itoroc/DetectorRadiacionRemoto/Diagramas_Electrónicos/ConsolaDeControl.kicad_sch

## KiCad design Diagramas_Electrónicos/ConsolaDeControl.kicad_sch (2025-11-12)

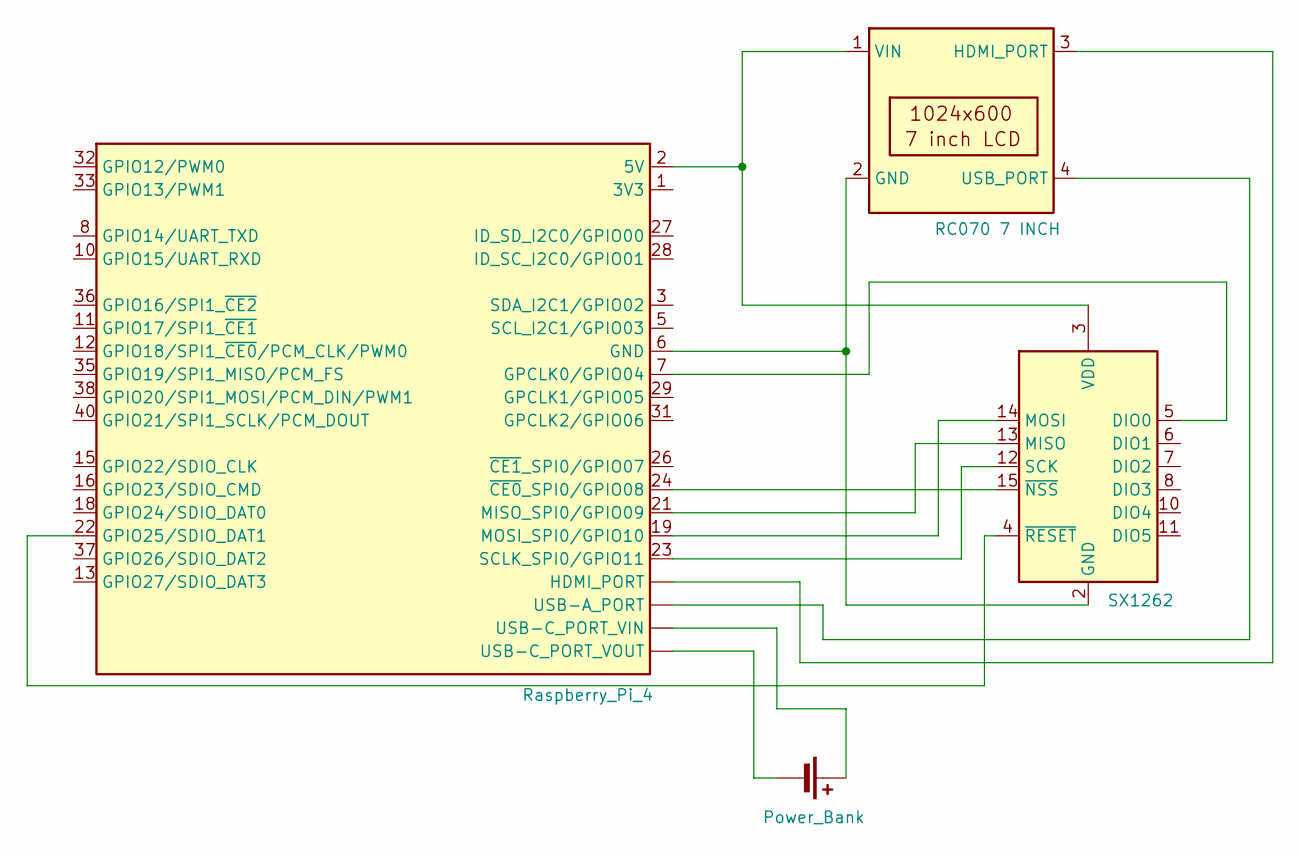
[picture p7: schematic ConsolaDeControl.kicad_sch]

Parts:
BT1: Power_Bank
J1: Raspberry_Pi_4
U1: RC070 7 INCH
U2: SX1262; Ai-Thinker-Ra-01-LoRa

Connections:
unnamed: BT1.1 (+), J1. (HDMI_PORT)
unnamed: BT1.2 (-), J1. (HDMI_PORT)
unnamed: J1.1 (3V3), J1.17 (3V3)
unnamed: J1.2 (5V), J1.4 (5V), U1.1 (VIN), U2.3 (VDD)
unnamed: J1.6 (GND), U1.2 (GND), U2.1 (GND), U2.2 (GND), U2.9 (GND), U2.16 (GND)
unnamed: J1.7 (GPCLK0/GPIO04), U2.5 (DIO0)
unnamed: J1.9 (GND), J1.14 (GND), J1.20 (GND), J1.25 (GND), J1.30 (GND), J1.34 (GND), J1.39 (GND)
unnamed: J1.19 (MOSI_SPI0/GPIO10), U2.14 (MOSI)
unnamed: J1.21 (MISO_SPI0/GPIO09), U2.13 (MISO)
unnamed: J1.22 (GPIO25/SDIO_DAT1), U2.4 (~RESET)
unnamed: J1.23 (SCLK_SPI0/GPIO11), U2.12 (SCK)
unnamed: J1.24 (~CE0_SPI0/GPIO08), U2.15 (~NSS)
unnamed: J1. (HDMI_PORT), U1.3 (HDMI_PORT), U1.4 (USB_PORT)
