itoroc/DetectorRadiacionRemoto/Diagramas_Electrónicos/DetectorRemoto.kicad_sch

## KiCad design Diagramas_Electrónicos/DetectorRemoto.kicad_sch (2025-11-12)

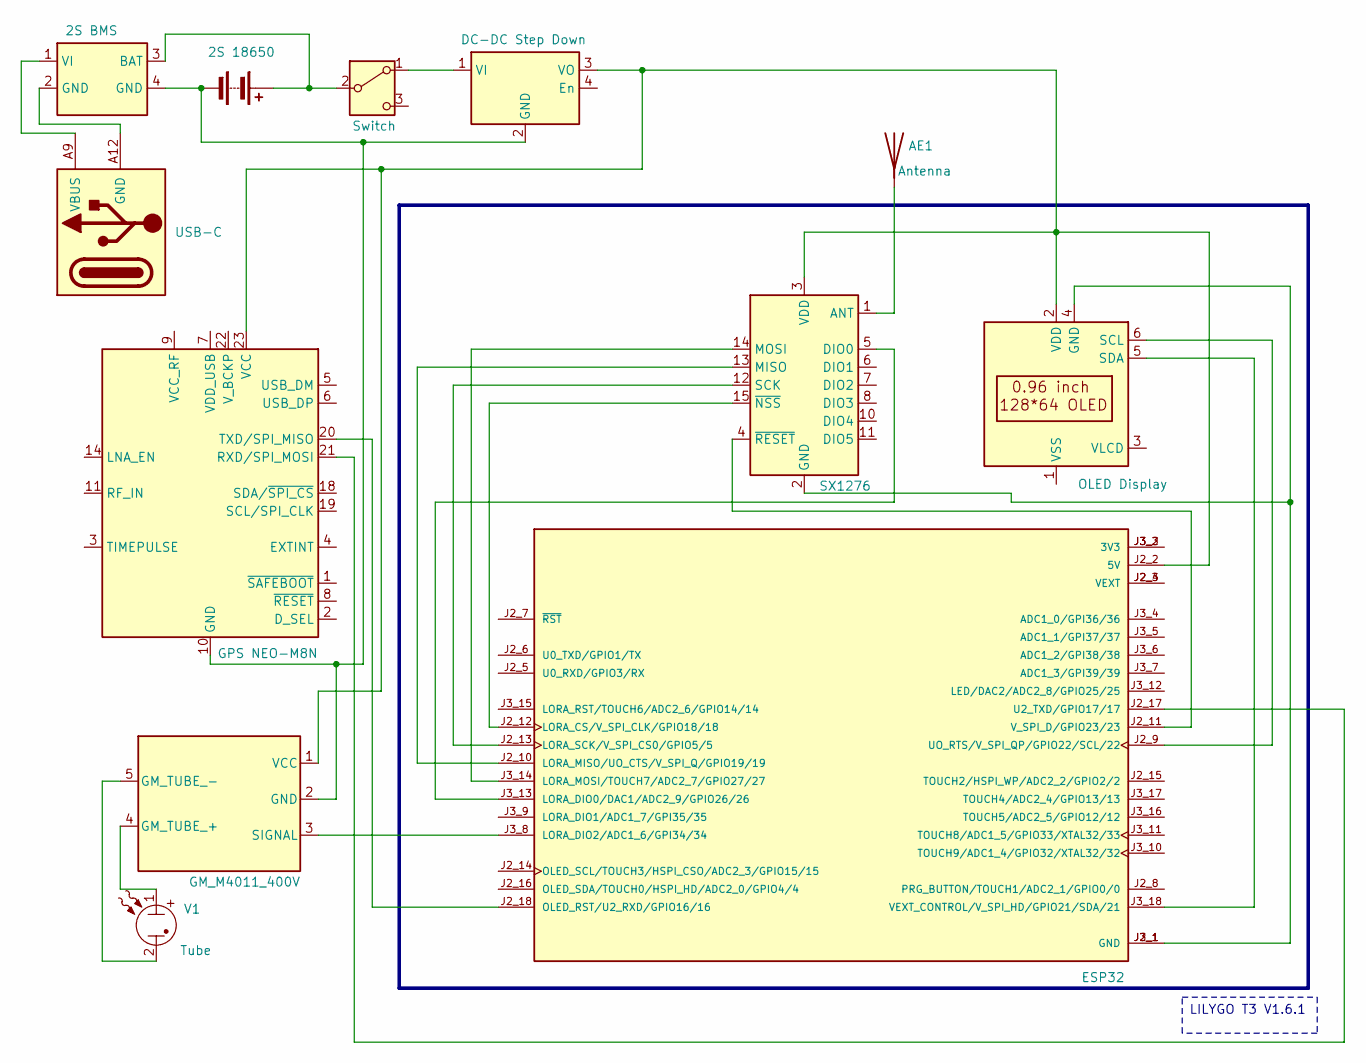
[picture p8: schematic DetectorRemoto.kicad_sch]

Parts:
AE1: Antenna
BT1: 2S 18650
J1: USB-C
SW1: Switch
U1: SX1276; Ai-Thinker-Ra-01-LoRa
U2: GPS NEO-M8N; ublox_NEO
U3: GM_M4011_400V; TO-220-4_Vertical
U4: ESP32; MODULE_ESP32_LORA_V2.0; PARTREV 2.0
U5: DC-DC Step Down; Texas_EUS_R-PDSS-T5_THT
U6: OLED Display; EA_T123X-I2C
U7: 2S BMS; Texas_EUS_R-PDSS-T5_THT
V1: Tube

Connections:
unnamed: AE1.1, U1.1 (ANT)
unnamed: BT1.1 (+), SW1.2 (B), U7.3 (BAT)
unnamed: BT1.2 (-), U2.10 (GND), U2.12 (GND), U2.13 (GND), U2.24 (GND), U3.2 (GND), U5.2 (GND), U7.4 (GND)
unnamed: J1.A9 (VBUS), U7.1 (VI)
unnamed: J1.A12 (GND), U7.2 (GND)
unnamed: SW1.1 (A), U5.1 (VI)
unnamed: U1.3 (VDD), U2.23 (VCC), U3.1 (VCC), U4.J2_2 (5V), U5.3 (VO), U6.2 (VDD)
unnamed: U1.4 (~RESET), U4.J2_11 (V_SPI_D/GPIO23/23)
unnamed: U1.5 (DIO0), U4.J3_13 (LORA_DIO0/DAC1/ADC2_9/GPIO26/26)
unnamed: U1.12 (SCK), U4.J2_13 (LORA_SCK/V_SPI_CS0/GPIO5/5)
unnamed: U1.13 (MISO), U4.J2_10 (LORA_MISO/UO_CTS/V_SPI_Q/GPIO19/19)
unnamed: U1.14 (MOSI), U4.J3_14 (LORA_MOSI/TOUCH7/ADC2_7/GPIO27/27)
unnamed: U1.15 (~NSS), U4.J2_12 (LORA_CS/V_SPI_CLK/GPIO18/18)
unnamed: U1.2 (GND), U1.9 (GND), U1.16 (GND), U4.J2_1 (GND), U4.J3_1 (GND), U6.4 (GND)
unnamed: U2.20 (TXD/SPI_MISO), U4.J2_18 (OLED_RST/U2_RXD/GPIO16/16)
unnamed: U2.21 (RXD/SPI_MOSI), U4.J2_17 (U2_TXD/GPIO17/17)
unnamed: U3.3 (SIGNAL), U4.J3_8 (LORA_DIO2/ADC1_6/GPI34/34)
unnamed: U3.4 (GM_TUBE_+), V1.1
unnamed: U3.5 (GM_TUBE_-), V1.2
unnamed: U4.J2_3 (VEXT), U4.J2_4 (VEXT)
unnamed: U4.J2_9 (UO_RTS/V_SPI_QP/GPIO22/SCL/22), U6.6 (SCL)
unnamed: U4.J3_2 (3V3), U4.J3_3 (3V3)
unnamed: U4.J3_18 (VEXT_CONTROL/V_SPI_HD/GPIO21/SDA/21), U6.5 (SDA)

Notes on the sheet:
LILYGO T3 V1.6.1
